robert-hh/Candle/candle/data_1.h

const PROGMEM  uint8_t bright[] = {
    132, 134, 139, 137, 133, 127, 124, 122, 119, 117, 137, 126, 115, 113, 119, 117, 125, 122, 100, 147, 
    139, 129, 121, 123, 126, 125, 120, 117, 115, 110, 125, 140, 145, 134, 126, 121, 115, 114, 114, 109, 
    115, 110, 128, 163, 110, 209, 195, 181, 158, 191, 135, 145, 144, 159, 120, 118, 122, 125, 116, 117, 
    115, 115, 115, 115, 113, 115, 118, 119, 119, 118, 107, 101, 81, 141, 115, 147, 142, 140, 118, 142, 
    153, 142, 117, 145, 115, 116, 137, 169, 114, 129, 125, 116, 108, 116, 117, 117, 117, 118, 114, 110, 
    112, 115, 117, 120, 122, 122, 122, 121, 121, 122, 120, 123, 126, 125, 115, 109, 108, 110, 112, 113, 
    131, 129, 120, 124, 127, 125, 121, 119, 117, 121, 120, 115, 100, 111, 115, 118, 107, 107, 116, 111, 
    117, 134, 158, 203, 161, 185, 132, 126, 144, 110, 113, 113, 117, 120, 118, 117, 117, 112, 104, 106, 
    109, 110, 114, 118, 117, 117, 114, 128, 141, 147, 134, 126, 122, 129, 147, 146, 126, 123, 117, 124, 
    120, 119, 126, 130, 123, 122, 125, 145, 161, 142, 129, 128, 130, 134, 131, 123, 115, 122, 131, 136, 
    127, 119, 122, 125, 129, 126, 128, 133, 135, 131, 129, 132, 127, 125, 124, 122, 121, 121, 122, 124, 
    122, 121, 122, 125, 127, 129, 129, 129, 128, 129, 130, 128, 125, 119, 117, 116, 118, 116, 123, 113, 
    118, 123, 155, 146, 139, 156, 135, 137, 124, 129, 122, 103, 104, 106, 113, 114, 123, 129, 126, 122, 
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
    149, 176, 171, 161, 147, 124, 109, 137, 122, 115, 111, 118, 125, 138, 135, 125, 117, 115, 116, 116, 
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
};
const PROGMEM uint16_t offset_tbl[] = {
0, 355, 707, 1059, 1412, 1764, 2117, 2469, 2821, 3173, 3525, 3878, 4239, 4595, 4950, 5307, 5665 
};
