robert-hh/Candle/candle/data_2.h

const PROGMEM  uint8_t bright[] = {
    126, 130, 136, 139, 142, 143, 134, 122, 107, 106, 108, 130, 144, 147, 149, 148, 148, 138, 130, 130, 
    132, 134, 134, 132, 132, 134, 137, 152, 148, 169, 126, 125, 125, 123, 123, 127, 128, 130, 129, 126, 
    127, 139, 139, 133, 135, 136, 131, 129, 130, 131, 134, 128, 117, 184, 176, 161, 117, 130, 145, 162, 
    142, 155, 126, 111, 111, 156, 175, 149, 126, 146, 143, 149, 149, 136, 126, 122, 123, 134, 132, 120, 
    110, 120, 123, 133, 157, 172, 154, 144, 138, 136, 137, 138, 125, 117, 125, 125, 125, 122, 124, 127, 
    132, 133, 135, 135, 131, 128, 125, 118, 96, 68, 132, 134, 161, 137, 145, 146, 125, 118, 126, 146, 
    147, 146, 147, 144, 141, 153, 147, 142, 171, 196, 199, 175, 202, 241, 175, 179, 188, 185, 161, 136, 
    158, 163, 148, 134, 129, 130, 128, 130, 132, 128, 130, 114, 88, 131, 114, 126, 117, 103, 109, 126, 
    108, 98, 65, 111, 141, 143, 158, 172, 186, 129, 176, 153, 159, 149, 136, 131, 129, 126, 121, 128, 
    108, 137, 157, 155, 160, 153, 146, 139, 119, 153, 150, 150, 130, 135, 103, 123, 117, 125, 132, 138, 
    142, 140, 133, 132, 130, 133, 138, 132, 126, 122, 122, 124, 122, 125, 125, 125, 124, 122, 124, 123, 
    123, 123, 124, 123, 124, 125, 127, 128, 131, 139, 142, 142, 139, 136, 136, 141, 143, 142, 144, 147, 
    144, 137, 144, 150, 147, 132, 113, 111, 136, 140, 153, 156, 136, 146, 153, 134, 136, 146, 163, 159, 
    136, 133, 128, 129, 133, 120, 153, 165, 160, 144, 136, 135, 133, 117, 125, 111, 91, 138, 155, 143, 
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
    98, 147, 155, 115, 107, 167, 158, 101, 105, 146, 157, 146, 150, 147, 166, 174, 161, 167, 144, 147, 
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
};
const PROGMEM uint16_t offset_tbl[] = {
0, 353, 705, 1063, 1415, 1767, 2121, 2473, 2828, 3180, 3532, 3889, 4241, 4593, 4953, 5310, 5664
};
