robert-hh/Candle/candle/data_4.h

const PROGMEM  uint8_t bright[] = {
    154, 154, 154, 154, 152, 154, 152, 151, 151, 153, 152, 151, 150, 147, 149, 148, 148, 146, 146, 147, 
    147, 145, 140, 139, 143, 140, 140, 142, 144, 147, 146, 146, 146, 146, 147, 147, 148, 150, 153, 155, 
    154, 150, 148, 142, 150, 161, 140, 161, 168, 175, 183, 172, 175, 173, 170, 170, 165, 156, 160, 156, 
    149, 151, 153, 158, 161, 158, 156, 157, 153, 150, 147, 151, 150, 147, 146, 150, 152, 154, 153, 153, 
    153, 153, 154, 152, 152, 150, 152, 151, 150, 150, 150, 149, 151, 150, 147, 149, 147, 147, 148, 148, 
    149, 147, 148, 148, 148, 148, 144, 143, 144, 143, 143, 141, 139, 140, 139, 140, 137, 137, 138, 137, 
    138, 140, 139, 139, 139, 139, 139, 140, 141, 142, 141, 141, 140, 141, 140, 141, 140, 142, 143, 144, 
    144, 141, 141, 141, 142, 140, 141, 141, 141, 140, 140, 139, 137, 138, 137, 137, 138, 137, 137, 137, 
    138, 138, 137, 137, 136, 138, 138, 141, 140, 142, 144, 144, 147, 144, 144, 146, 147, 148, 146, 148, 
    147, 147, 147, 147, 145, 141, 140, 136, 140, 149, 160, 164, 165, 165, 170, 172, 179, 181, 177, 171, 
    165, 160, 160, 179, 161, 143, 158, 160, 138, 126, 122, 124, 134, 134, 148, 161, 163, 151, 155, 169, 
    183, 192, 193, 206, 205, 162, 147, 170, 177, 162, 148, 145, 146, 146, 146, 157, 167, 180, 188, 193, 
    197, 185, 164, 161, 162, 153, 154, 170, 176, 182, 179, 171, 164, 158, 154, 154, 154, 158, 158, 160, 
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
    151, 157, 163, 161, 161, 160, 154, 151, 146, 144, 142, 140, 139, 137, 137, 139, 142, 141, 140, 135, 
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
};
const PROGMEM uint16_t offset_tbl[] = {
12, 364, 717, 1074, 1437, 1796, 2151, 2504, 2881, 3246, 3601, 3953, 4305, 4664, 5023, 5375, 5727 
};
