robert-hh/Candle/candle/data_4q.h

const PROGMEM  uint8_t bright[] = {
    148, 148, 148, 148, 147, 148, 147, 145, 146, 147, 146, 146, 144, 141, 144, 142, 142, 140, 140, 142, 
    141, 140, 134, 133, 137, 134, 134, 136, 138, 141, 140, 140, 140, 140, 141, 141, 143, 144, 148, 149, 
    148, 144, 143, 136, 144, 156, 134, 156, 163, 170, 179, 167, 170, 168, 164, 165, 160, 151, 154, 151, 
    144, 146, 148, 152, 156, 153, 150, 151, 148, 145, 142, 145, 144, 141, 140, 144, 146, 148, 148, 147, 
    148, 148, 148, 147, 146, 144, 146, 146, 144, 144, 145, 144, 145, 144, 142, 143, 142, 141, 142, 142, 
    143, 142, 143, 142, 142, 142, 139, 137, 138, 137, 137, 135, 133, 134, 133, 134, 131, 132, 132, 132, 
    133, 134, 133, 133, 133, 133, 133, 134, 135, 136, 135, 135, 134, 135, 134, 136, 134, 136, 137, 138, 
    139, 136, 135, 135, 136, 134, 135, 135, 135, 134, 134, 133, 131, 132, 131, 131, 132, 131, 131, 132, 
    132, 132, 132, 131, 130, 132, 132, 135, 134, 136, 139, 139, 141, 138, 138, 140, 142, 143, 140, 142, 
    142, 141, 141, 141, 140, 135, 134, 130, 134, 144, 155, 159, 160, 160, 165, 167, 174, 176, 172, 166, 
    160, 155, 154, 174, 156, 137, 152, 154, 133, 120, 116, 118, 128, 129, 142, 156, 157, 146, 150, 164, 
    178, 188, 189, 202, 201, 157, 141, 164, 172, 156, 142, 140, 140, 140, 140, 151, 161, 175, 184, 188, 
    193, 180, 159, 156, 156, 147, 148, 164, 171, 178, 174, 166, 158, 152, 149, 149, 149, 152, 153, 155, 
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
    146, 152, 157, 156, 156, 154, 149, 146, 140, 139, 136, 134, 133, 132, 132, 133, 136, 136, 134, 129, 
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
};
const PROGMEM uint16_t offset_tbl[] = {
7, 360, 720, 1075, 1437, 1797, 2155, 2507, 2881, 3246, 3601, 3953, 4305, 4664, 5023, 5375, 5727
};
