robert-hh/Candle/candle/data_4qq.h

const PROGMEM  uint8_t bright[] = {
    142, 143, 143, 142, 141, 142, 141, 139, 140, 141, 140, 140, 138, 135, 138, 136, 136, 135, 134, 136, 
    135, 134, 128, 127, 131, 128, 128, 131, 132, 135, 134, 135, 135, 135, 135, 135, 137, 138, 142, 144, 
    142, 139, 137, 131, 139, 150, 128, 150, 158, 165, 174, 162, 165, 162, 159, 160, 154, 145, 149, 145, 
    138, 140, 142, 147, 150, 147, 144, 145, 142, 139, 136, 139, 139, 135, 135, 138, 140, 142, 142, 141, 
    142, 142, 142, 141, 140, 139, 140, 140, 138, 138, 139, 138, 139, 139, 136, 137, 136, 135, 136, 136, 
    137, 136, 137, 136, 136, 136, 133, 131, 132, 131, 131, 129, 127, 128, 127, 128, 125, 126, 126, 126, 
    127, 128, 127, 127, 127, 127, 127, 128, 129, 131, 129, 129, 128, 129, 128, 130, 128, 131, 131, 132, 
    133, 130, 129, 129, 130, 128, 129, 129, 129, 128, 128, 127, 125, 126, 125, 125, 126, 125, 125, 126, 
    126, 126, 126, 125, 124, 126, 126, 129, 128, 130, 133, 133, 135, 132, 132, 135, 136, 137, 135, 136, 
    136, 135, 135, 135, 134, 129, 128, 124, 128, 138, 149, 153, 154, 154, 160, 162, 169, 171, 166, 160, 
    154, 149, 149, 169, 150, 131, 147, 149, 127, 114, 110, 112, 122, 123, 136, 150, 152, 140, 144, 158, 
    173, 183, 184, 198, 197, 151, 135, 159, 167, 151, 136, 134, 134, 134, 135, 145, 156, 170, 179, 184, 
    189, 175, 153, 150, 151, 141, 142, 159, 166, 173, 169, 161, 153, 147, 143, 143, 143, 147, 147, 149, 
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
    140, 146, 152, 150, 150, 149, 143, 140, 135, 133, 131, 128, 127, 126, 126, 127, 131, 130, 128, 123, 
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
};
const PROGMEM uint16_t offset_tbl[] = {
7, 360, 720, 1075, 1437, 1797, 2155, 2507, 2881, 3246, 3601, 3953, 4305, 4664, 5023, 5375, 5727 
};
