robert-hh/Candle/candle/data_7f1.h

const PROGMEM  uint8_t bright[] = {
    213, 210, 205, 203, 208, 211, 214, 215, 215, 214, 211, 204, 188, 180, 180, 189, 197, 200, 198, 190, 
    172, 156, 167, 182, 192, 199, 200, 190, 169, 141, 153, 198, 201, 192, 183, 180, 151, 108, 88, 117, 
    127, 155, 189, 205, 210, 215, 221, 224, 228, 233, 237, 236, 232, 234, 235, 232, 229, 226, 224, 223, 
    223, 225, 226, 227, 227, 228, 227, 226, 226, 226, 224, 220, 217, 215, 216, 218, 220, 221, 221, 219, 
    215, 214, 214, 213, 214, 214, 212, 211, 211, 212, 214, 217, 218, 217, 211, 215, 207, 201, 200, 198, 
    205, 208, 196, 184, 179, 181, 188, 211, 224, 227, 231, 228, 194, 145, 146, 155, 166, 168, 161, 191, 
    203, 198, 198, 201, 206, 209, 203, 187, 177, 181, 175, 166, 156, 134, 110, 103, 155, 177, 181, 152, 
    116, 78, 47, 69, 129, 189, 205, 194, 169, 139, 126, 105, 75, 55, 46, 67, 113, 153, 169, 171, 
    203, 204, 174, 188, 158, 131, 95, 176, 219, 162, 50, 123, 71, 14, 13, 150, 136, 161, 179, 202, 
    201, 168, 153, 145, 101, 95, 110, 152, 163, 186, 202, 140, 113, 70, 27, 32, 44, 47, 10, 3, 
    1, 4, 9, 25, 69, 91, 71, 100, 118, 122, 128, 99, 66, 140, 94, 81, 107, 118, 140, 162, 
    160, 169, 185, 193, 191, 189, 186, 179, 172, 167, 169, 181, 166, 136, 140, 162, 192, 206, 212, 214, 
    215, 216, 215, 215, 217, 217, 217, 219, 220, 221, 222, 221, 220, 216, 215, 216, 217, 217, 219, 218, 
    216, 216, 216, 216, 217, 217, 218, 218, 218, 219, 219, 219, 220, 221, 222, 223, 224, 225, 226, 227, 
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
    236, 255, 225, 217, 211, 208, 211, 209, 200, 192, 189, 189, 185, 175, 176, 189, 203, 205, 202, 198, 
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
};
const PROGMEM uint16_t offset_tbl[] = {
2, 366, 718, 1097, 1450, 1802, 2154, 2506, 2858, 3210, 3564, 3921, 4273, 4625, 4980, 5332, 5684
};
