robert-hh/Candle/candle/data_7f2.h

const PROGMEM  uint8_t bright[] = {
    112, 138, 166, 170, 156, 128, 113, 109, 115, 123, 140, 161, 185, 192, 192, 187, 180, 175, 173, 183, 
    197, 207, 211, 199, 192, 184, 182, 197, 215, 221, 219, 196, 172, 182, 187, 199, 223, 226, 225, 216, 
    210, 193, 158, 118, 108, 105, 73, 53, 37, 15, 4, 5, 5, 2, 6, 18, 34, 50, 66, 77, 
    69, 57, 44, 36, 41, 50, 55, 60, 66, 78, 115, 138, 141, 144, 137, 123, 112, 108, 114, 122, 
    132, 137, 138, 138, 137, 136, 138, 142, 139, 138, 126, 111, 107, 117, 128, 132, 158, 166, 160, 163, 
    142, 133, 161, 179, 176, 174, 154, 116, 104, 112, 108, 128, 193, 226, 215, 207, 197, 196, 202, 161, 
    143, 163, 165, 158, 154, 154, 170, 192, 203, 199, 203, 213, 220, 226, 227, 229, 226, 222, 219, 225, 
    227, 227, 233, 229, 223, 204, 186, 205, 219, 225, 227, 227, 228, 228, 229, 228, 221, 211, 214, 215, 
    204, 176, 193, 178, 219, 226, 233, 223, 101, 193, 223, 208, 211, 235, 247, 201, 215, 185, 175, 148, 
    139, 200, 212, 218, 231, 230, 223, 216, 216, 202, 203, 217, 222, 227, 222, 223, 230, 221, 219, 238, 
    227, 224, 228, 229, 222, 221, 221, 217, 220, 218, 225, 232, 220, 238, 242, 225, 222, 231, 234, 228, 
    224, 220, 217, 212, 218, 220, 220, 218, 220, 215, 210, 205, 218, 227, 222, 206, 182, 161, 146, 137, 
    133, 132, 140, 151, 149, 155, 156, 147, 134, 124, 118, 116, 137, 165, 168, 164, 158, 153, 149, 155, 
    164, 166, 164, 158, 152, 148, 146, 145, 144, 144, 143, 138, 126, 115, 110, 100, 87, 78, 70, 70, 
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
    26, 23, 170, 161, 171, 179, 169, 171, 188, 197, 201, 198, 204, 214, 214, 200, 189, 184, 186, 192, 
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
};
const PROGMEM uint16_t offset_tbl[] = {
12, 365, 719, 1123, 1479, 1894, 2255, 2612, 2967, 3319, 3673, 4026, 4378, 4736, 5091, 5443, 5840
};
